dropenmind/AIS-wifi-bridge/images/NMEA-Bridge16.png

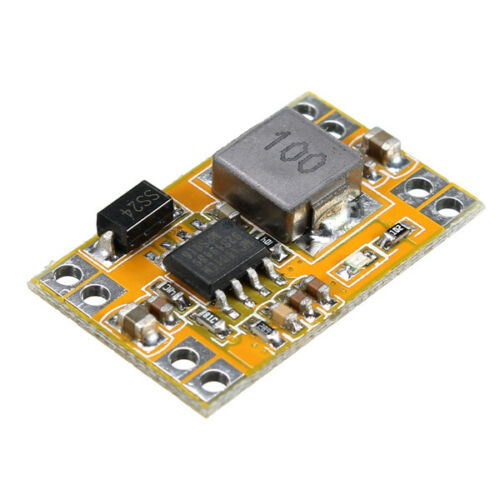
images/NMEA-Bridge16.png
